RadHiveFun/18650-3S-Battery-Pack/media files/assembled/IMG_20260920_213753_0_2026-09-20_21-56-50_856.jpg

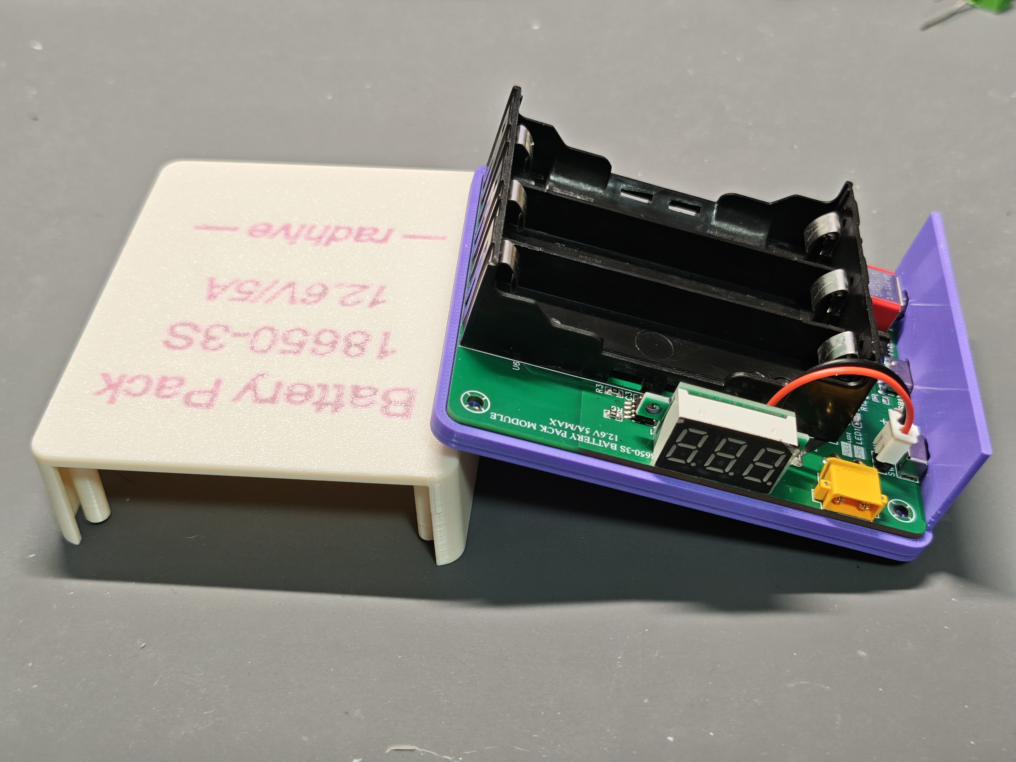
media files/assembled/IMG_20260920_213753_0_2026-09-20_21-56-50_856.jpg
