RadHiveFun/18650-3S-Battery-Pack/media files/assembled/IMG_20260920_213808_1_2026-09-20_21-56-50_871.jpg

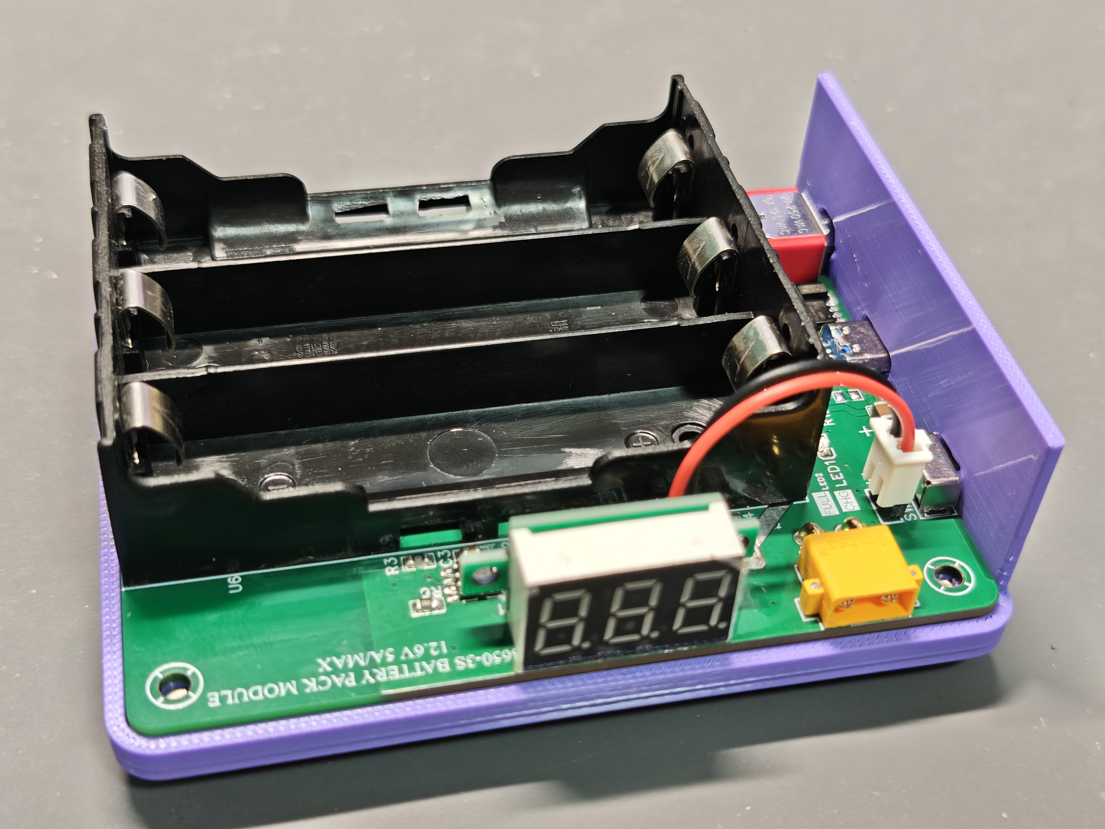
media files/assembled/IMG_20260920_213808_1_2026-09-20_21-56-50_871.jpg
