RadHiveFun/18650-3S-Battery-Pack/media files/assembling/DSC04766.JPG

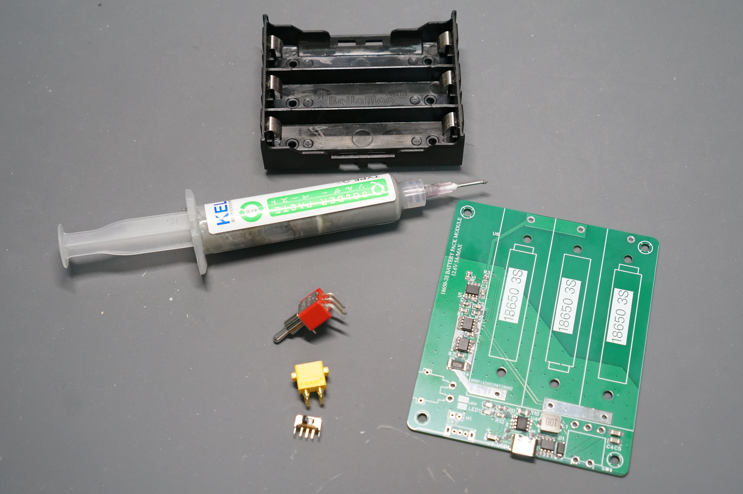
media files/assembling/DSC04766.JPG
